mazgch/hpg/docu/CaptivePortal.png

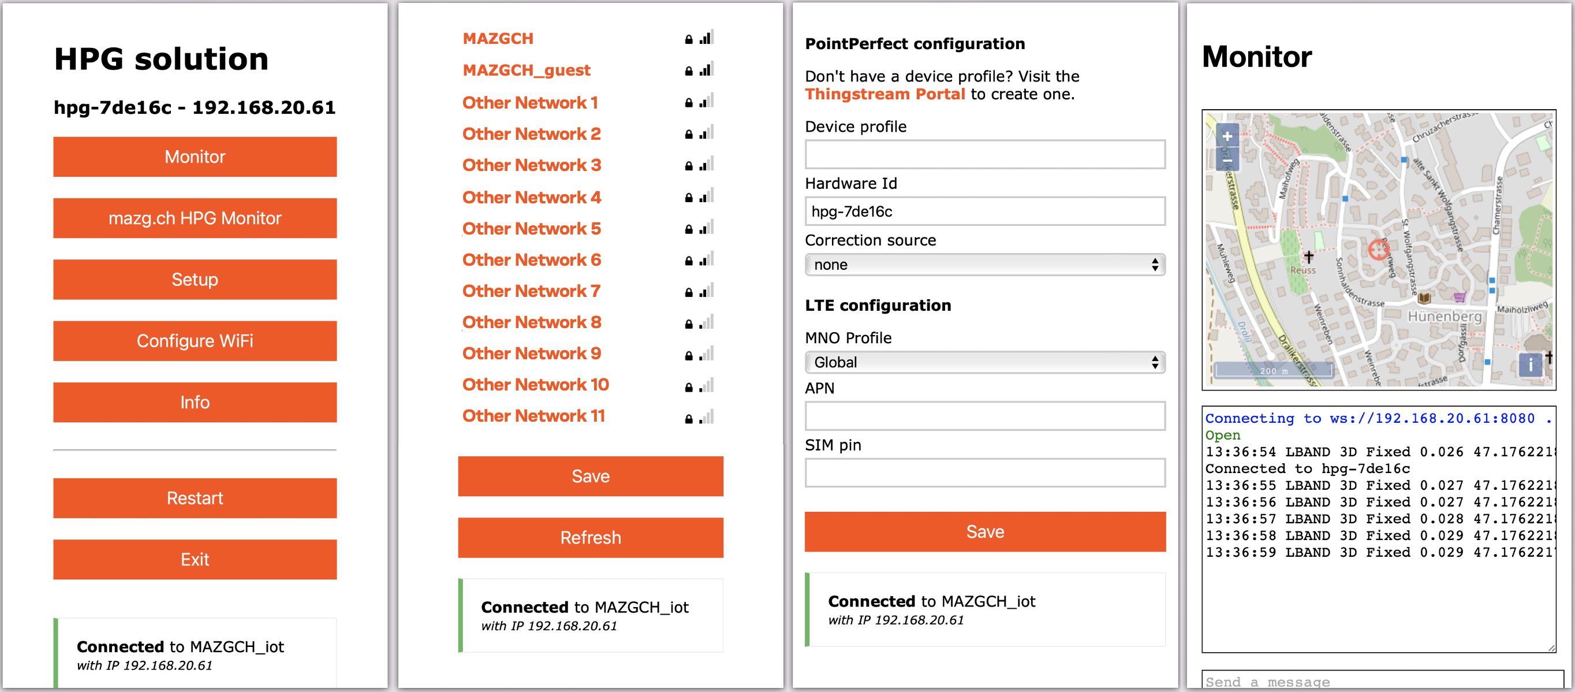
docu/CaptivePortal.png
